k-moskwa/kmSigGen/kmSigGenEagle/kmSigGenTiny_PCB_1L_B.png

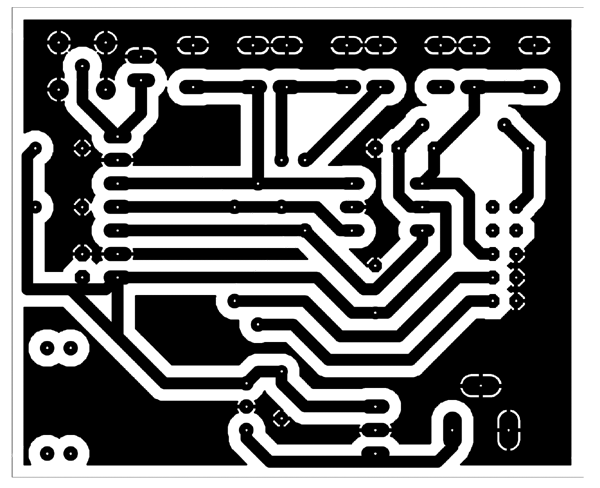
kmSigGenEagle/kmSigGenTiny_PCB_1L_B.png
