k-moskwa/kmSigGen/kmSigGenEagle/kmSigGenTiny_PCB_1L_View.PNG

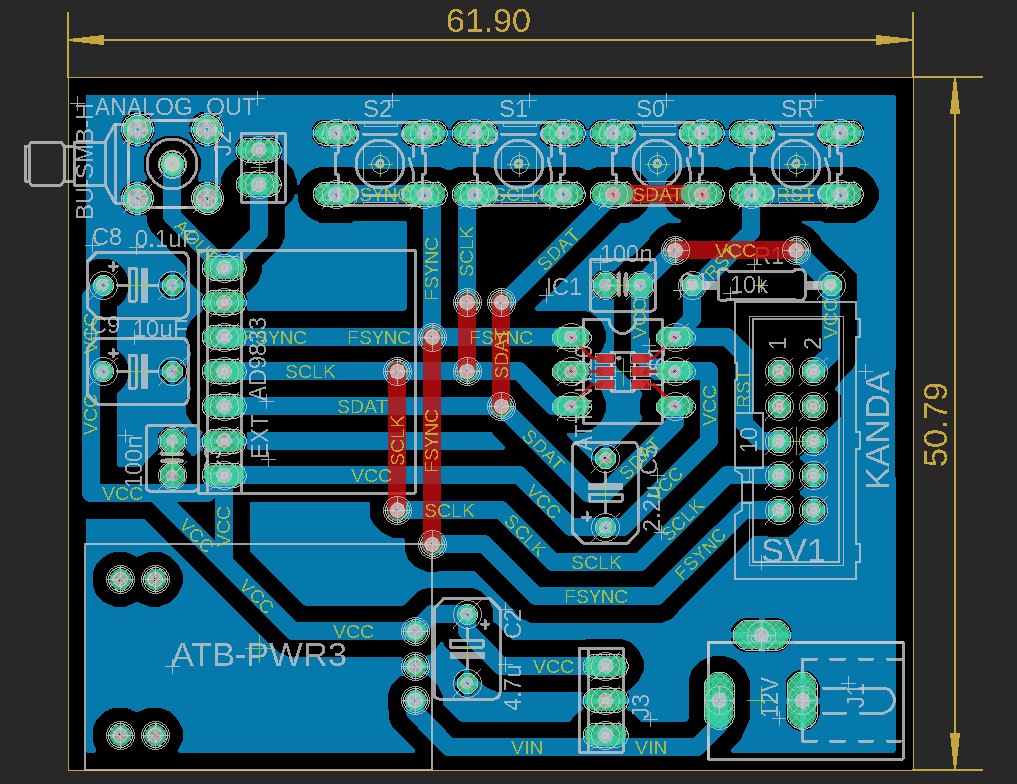
kmSigGenEagle/kmSigGenTiny_PCB_1L_View.PNG
